samuelclay/grove/firmware/main/src/grove.h

#include <OctoWS2811.h>
#include <avr/power.h>
#include <SPI.h>
#include <QuadraticEase.h>
#include <SineEase.h>

#define CAMPLIGHTS
// #define RANDOMBREATHS
// #define FAKE_PIR

// ===================
// = Pin Definitions =
// ===================

const uint8_t treeAPin = 14;
const int slaveSelectPin = 10;
// #define HWSERIAL Serial1
#define PIR1_PIN 9
#define PIR2_PIN 12

#define PIR_REMOTE_PIN 0
#define BREATH_REMOTE_PIN 1

long lastRemoteBreathRead = 0;
const long remoteBreathReadInteval = 20;

bool isBreath = false;

// ===========
// = Globals =
// ===========

#ifdef CAMPLIGHTS
const int32_t REST_DRIP_WIDTH_MIN = 10000;
const int32_t REST_DRIP_WIDTH_MAX = 100000;
const int ledsPerStrip = 720;
#else
const int32_t REST_DRIP_WIDTH_MIN = 4;
const int32_t REST_DRIP_WIDTH_MAX = 80;
const int ledsPerStrip = 720;
#endif
const int32_t REST_DRIP_DELAY_MIN = 10;
const int32_t REST_DRIP_DELAY_MAX = 50;

const int32_t BASE_PIR_FADE_IN = 2000;
const int32_t BASE_PIR_FADE_OUT = 5000;

// A single 1m strip is 144 LEDs/m. 720 = 5m.
// const int ledsPerStrip = 432;

DMAMEM int displayMemory[ledsPerStrip*6];
int drawingMemory[ledsPerStrip*6];
const int config = WS2811_GRB | WS2811_800kHz;


// Amount of color fade from front-to-back of each drip.
// Can probably increase this to 0.64 during Burning Man.
const double REST_DRIP_DECAY = 0.64;
const double BREATH_DECAY = 0.95;

// Time taken for drip to traverse LEDs
#ifdef CAMPLIGHTS
const unsigned long REST_DRIP_TRIP_MS = 20000;
#else
const unsigned long REST_DRIP_TRIP_MS = 60000;
#endif
const unsigned long BREATH_TRIP_MS = 20000;
const unsigned long BREATH_RISE_MS = 2750;

uint32_t dripCount = 0;
uint32_t breathCount = 0;

// This limit is responsible for how much memory the drips take.
const int DRIP_LIMIT = 20;
unsigned long dripStarts[DRIP_LIMIT];
unsigned int dripColors[DRIP_LIMIT];
unsigned int dripWidth[DRIP_LIMIT];
bool dripEaten[DRIP_LIMIT];
unsigned long newDripDelayEnd = 0;

const int BREATH_LIMIT = 20;
unsigned long breathStarts[BREATH_LIMIT];
unsigned int breathWidth[BREATH_LIMIT];
unsigned int breathPosition[BREATH_LIMIT];
int activeBreath = -1;
unsigned long lastNewBreathMs = 0;
unsigned long endActiveBreathMs = 0;
int furthestBreathPosition = 0;
unsigned long breathBoostStart = 0;
unsigned long breathFallingStart = 0;
bool detectedBreath = false;

QuadraticEase dripEase[DRIP_LIMIT];
QuadraticEase breathEase[BREATH_LIMIT];

// High current Leaves
const int LEAVES_REST_MS = 2000;

typedef enum
{
    STATE_RESTING  = 0,
    STATE_RISING   = 1,
    STATE_FALLING  = 2
} state_breath_t;
state_breath_t breathState;

typedef enum
{
    STATE_PIR_INACTIVE  = 0,
    STATE_PIR_ACTIVE  = 1,
} state_proximity_t;
state_proximity_t proximityState;

unsigned long pirStart = 0;
unsigned long pirEnd = 0;

// ========
// = LEDs =
// ========

OctoWS2811 leds(ledsPerStrip, displayMemory, drawingMemory, config);

// ========
// = SPI =
// ========

SPISettings dispatcherSPISettings(1e6, MSBFIRST, SPI_MODE3); 

// PIR

#define PIR_COUNT 2
#define PIR_HIST_LEN 10

const long pirSampleInterval = 20;
long lastPIRSampleTime[PIR_COUNT];
int pirHistoryIndex[PIR_COUNT];
int pirHistory[PIR_COUNT][PIR_HIST_LEN];

typedef enum {
	PIR_ON,
	PIR_OFF
} PirState;

PirState pir1State = PIR_OFF;
PirState pir2State = PIR_OFF;
long openTimeoutLastEvent = 0;
const long openTimeout = 5*1000;

typedef enum {
	STATE_NEUTRAL,
	STATE_OPEN
} SystemState;

SystemState overallState = STATE_NEUTRAL;

// =============
// = Functions =
// =============

void drawDrip(int d, int dripStart, int color);
void drawBreath(int b, int breathStart);
void addRandomDrip();
void addBreath();
void advanceRestDrips();
void advanceBreaths();
unsigned long randomGreen();
void dispatcher(uint8_t chan, uint8_t value);
void clearDispatcher();
void testDispatcherRGB(int delayTime);
void setDispatcherGlobalRGB(uint8_t rValue, uint8_t gValue, uint8_t bValue);
uint8_t flipByte(uint8_t val);
void runLeaves();
void runBase();
void transmitSensor();
void receiveSensor();
void updatePIR(int p);

/**   
* \par   
* Sine Table is generated from following loop   
* <pre>for(i = 0; i < 360; i++)   
* {   
*    sinTable[i]= sin((i-180) * PI/180.0);   
* } </pre>   
*/


static const float sinTable[360] = {
  -0.017452406437283439f, -0.034899496702500699f, -0.052335956242943807f,
  -0.069756473744125524f, -0.087155742747658638f, -0.104528463267653730f,
  -0.121869343405147550f, -0.139173100960065740f,
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
  -0.422618261740699330f, -0.406736643075800100f, -0.390731128489273600f,
  -0.374606593415912070f, -0.358367949545300270f, -0.342020143325668710f,
  -0.325568154457156420f, -0.309016994374947340f,
  -0.292371704722736660f, -0.275637355816999050f, -0.258819045102520850f,
  -0.241921895599667790f, -0.224951054343864810f, -0.207911690817759120f,
  -0.190808995376544800f, -0.173648177666930300f,
  -0.156434465040231040f, -0.139173100960065350f, -0.121869343405147370f,
  -0.104528463267653330f, -0.087155742747658235f, -0.069756473744125330f,
  -0.052335956242943620f, -0.034899496702500733f,
  -0.017452406437283477f, 0.000000000000000061f, 0.017452406437283376f,
  0.034899496702501080f, 0.052335956242943966f, 0.069756473744125455f,
  0.087155742747658138f, 0.104528463267653460f,
  0.121869343405147490f, 0.139173100960065690f, 0.156434465040230920f,
  0.173648177666930410f, 0.190808995376544920f, 0.207911690817759450f,
  0.224951054343864920f, 0.241921895599667900f,
  0.258819045102520740f, 0.275637355816999160f, 0.292371704722736770f,
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
};
